huexpub/IRMQTT/pic/DSC_4234.JPG

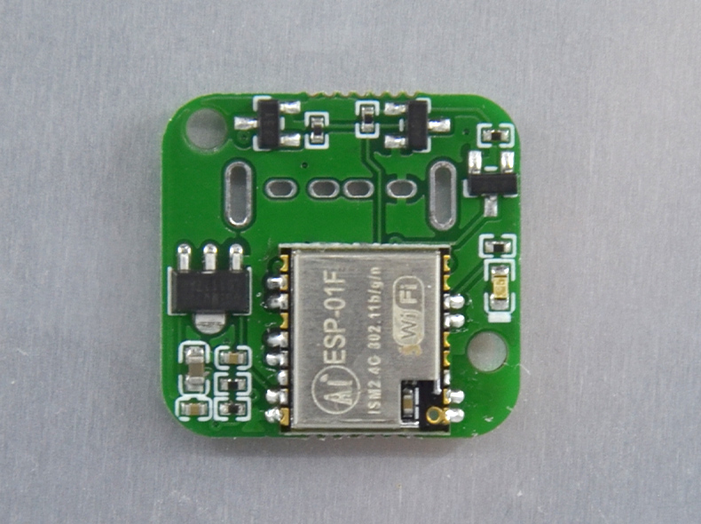
pic/DSC_4234.JPG
